themaxbang/MRIYA/pictures/mriya_02.jpeg

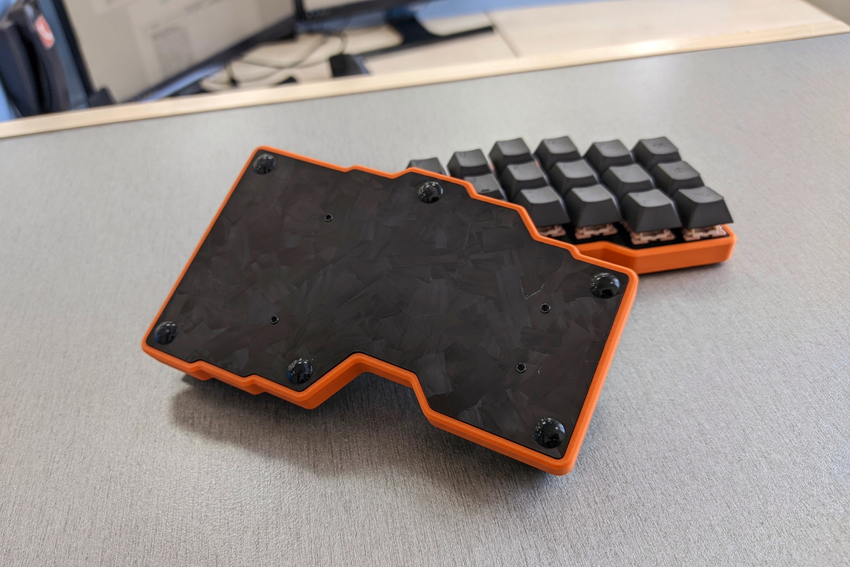
pictures/mriya_02.jpeg
