themaxbang/MRIYA/pictures/mriya_03.jpeg

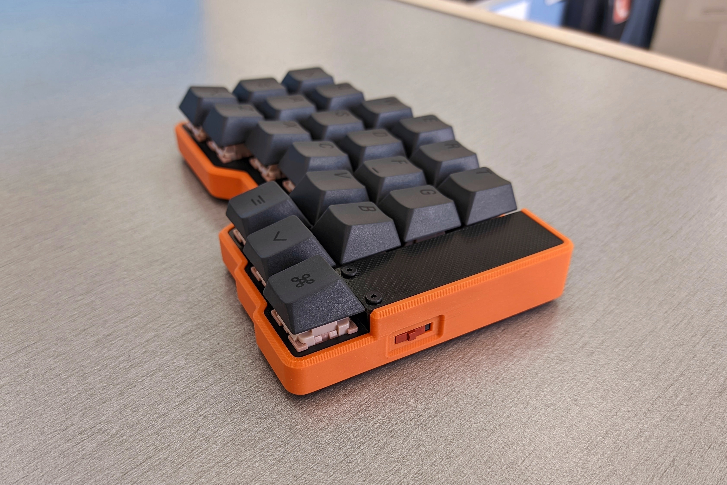
pictures/mriya_03.jpeg
