themaxbang/MRIYA/pictures/mriya_04.jpeg

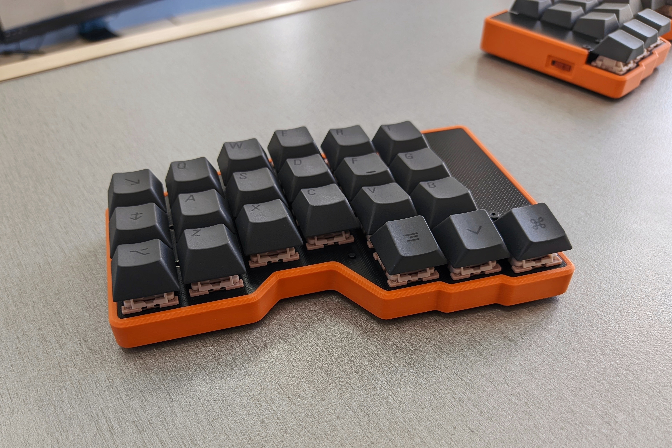
pictures/mriya_04.jpeg
