themaxbang/MRIYA/pictures/mriya_06.jpeg

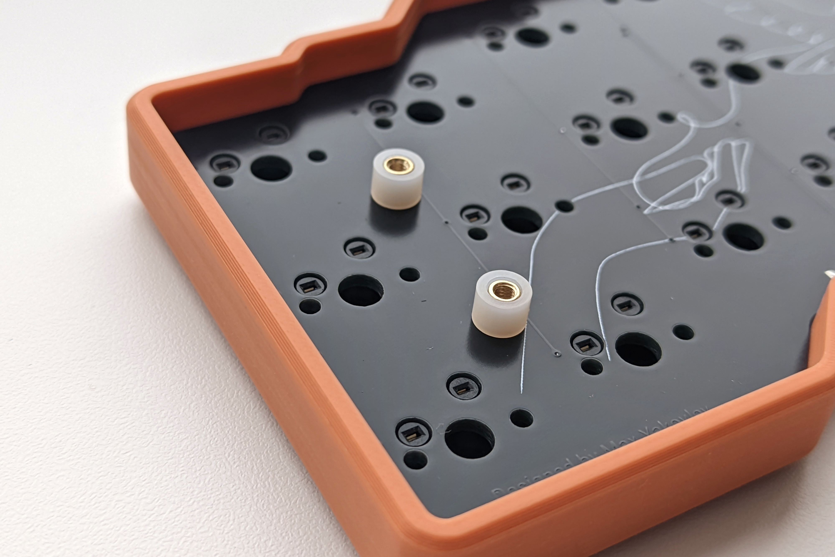
pictures/mriya_06.jpeg
