themaxbang/MRIYA/pictures/mriya_07.jpeg

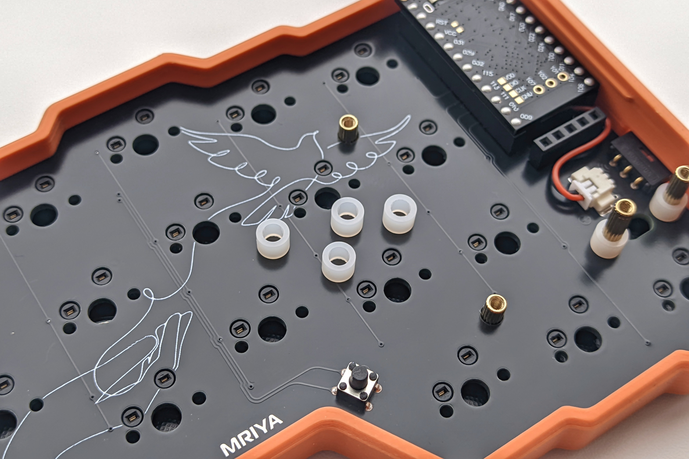
pictures/mriya_07.jpeg
