themaxbang/MRIYA/pictures/mriya_08.jpeg

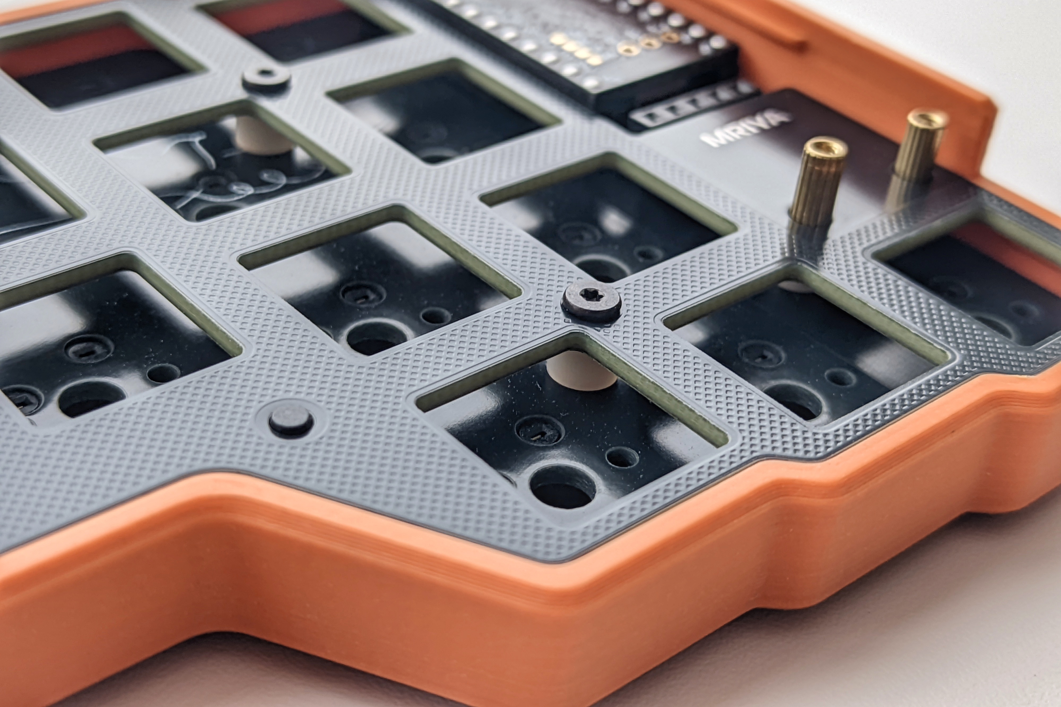
pictures/mriya_08.jpeg
