themaxbang/MRIYA/pictures/mriya_09.jpeg

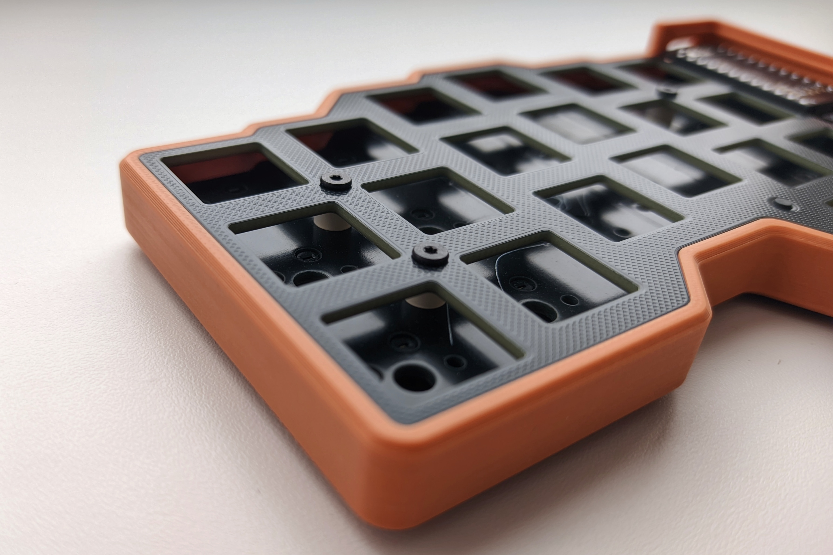
pictures/mriya_09.jpeg
