themaxbang/MRIYA/pictures/mriya_10.jpeg

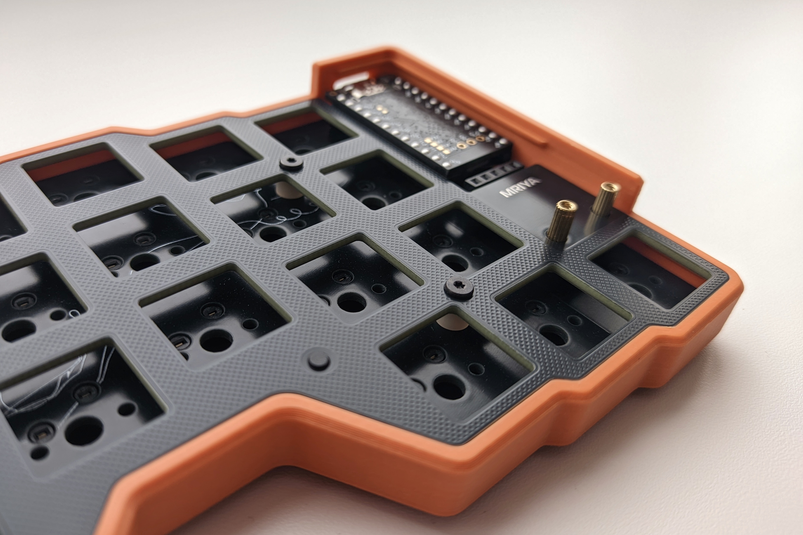
pictures/mriya_10.jpeg
