themaxbang/MRIYA/pictures/mriya_11.jpeg

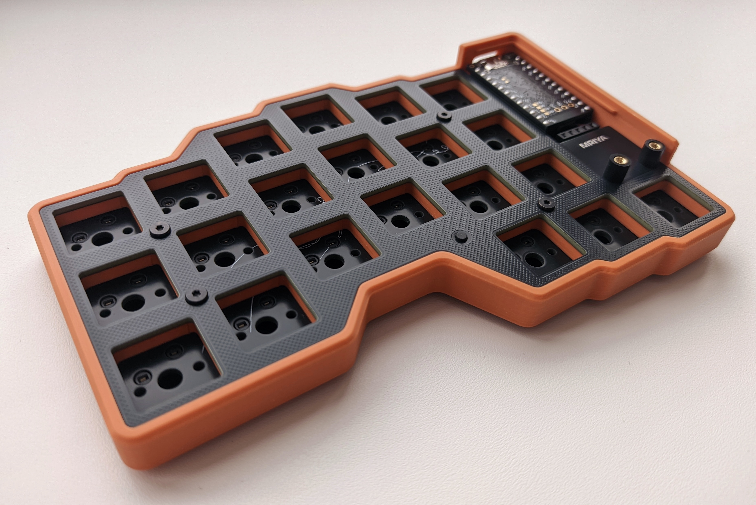
pictures/mriya_11.jpeg
