themaxbang/MRIYA/pictures/mriya_12.jpeg

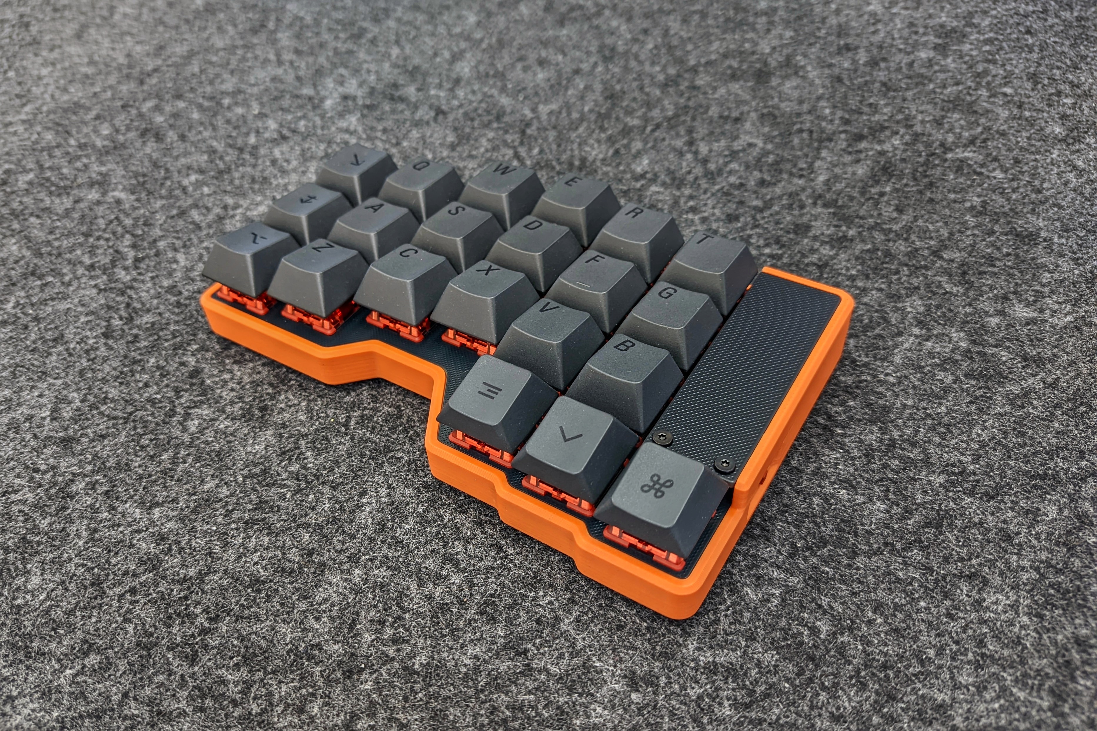
pictures/mriya_12.jpeg
