themaxbang/MRIYA/pictures/mriya_13.jpeg

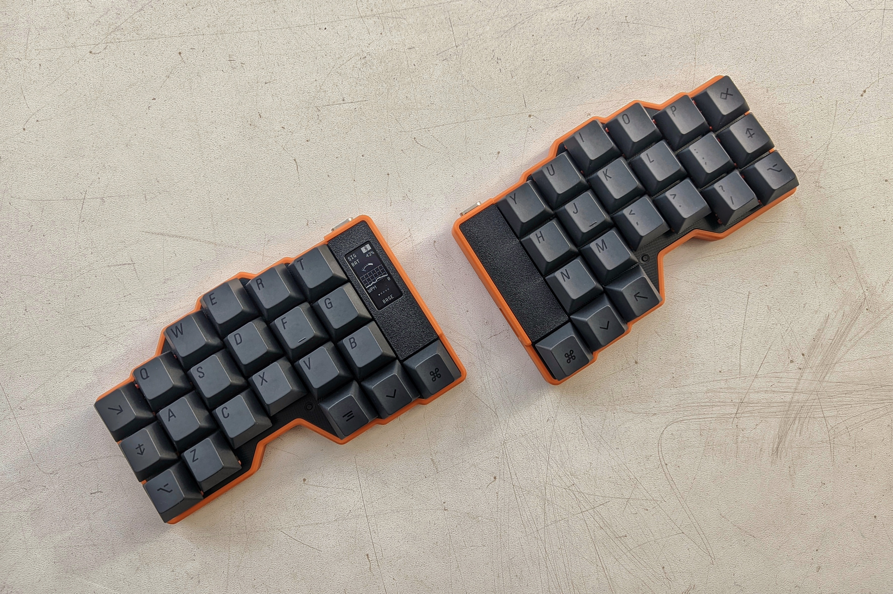
pictures/mriya_13.jpeg
