themaxbang/MRIYA/pictures/mriya_14.jpeg

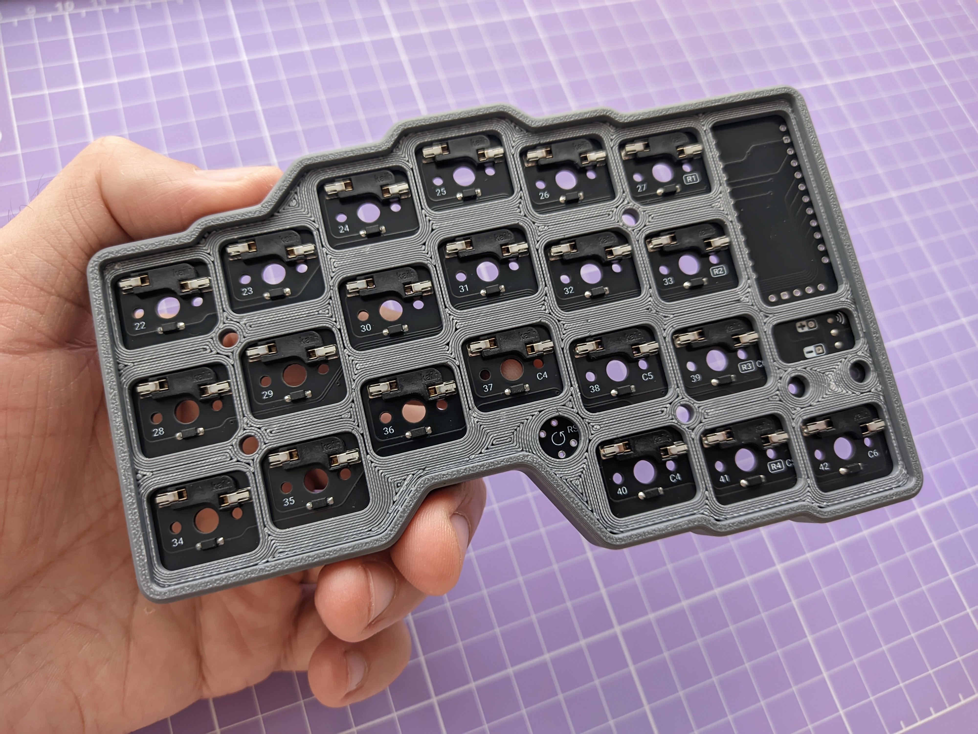
pictures/mriya_14.jpeg
