themaxbang/MRIYA/renders/mriya-bsi-10h-molex.png

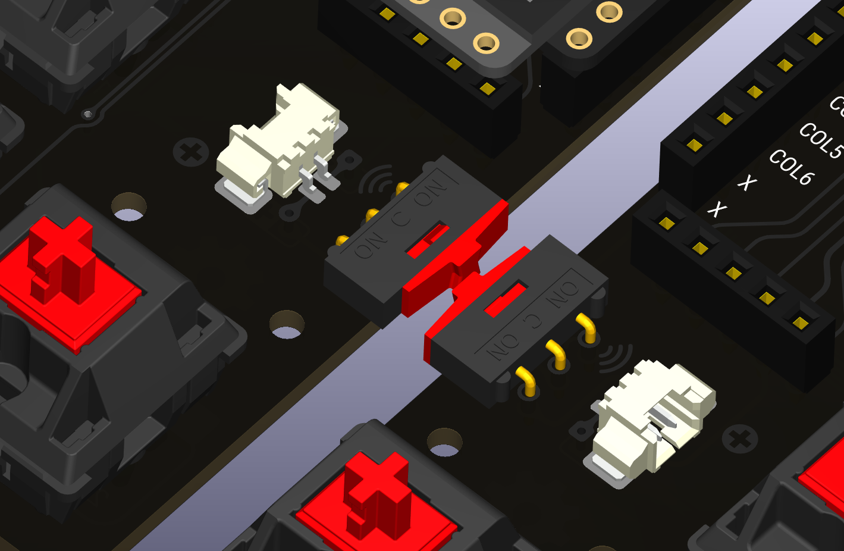
renders/mriya-bsi-10h-molex.png
