themaxbang/MRIYA/renders/mriya-mcu-cover.png

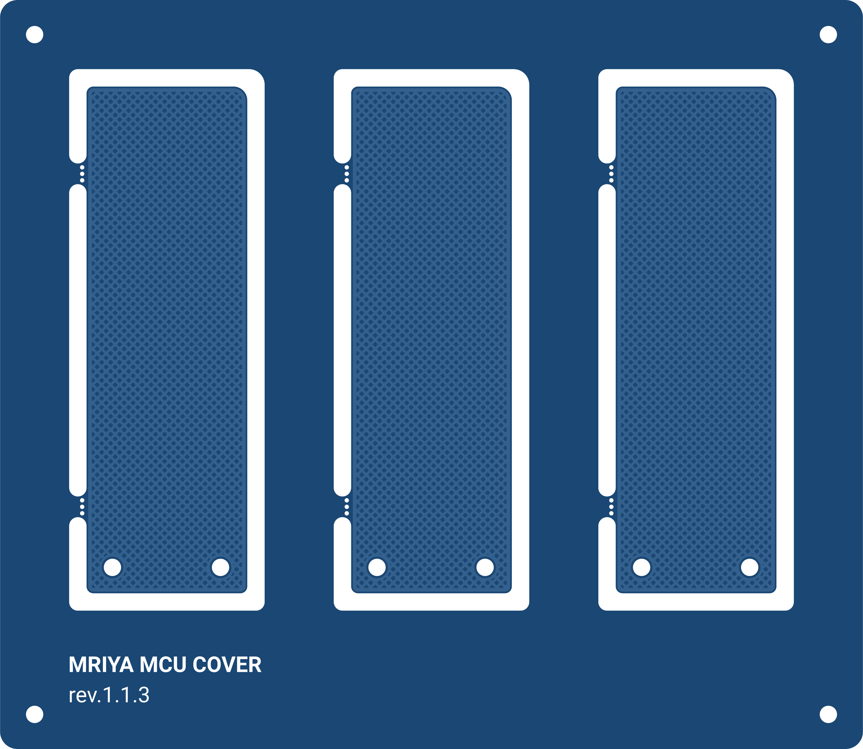
renders/mriya-mcu-cover.png
