themaxbang/MRIYA/case/CNC (not tested)/02 mcu cover/mriya-cnc-display-cover-v1.01.step

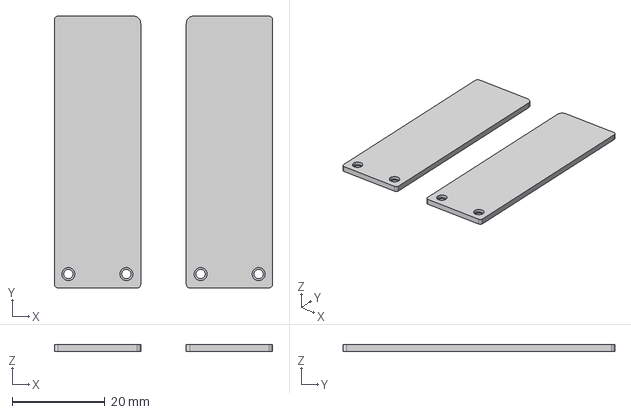
[picture p40: CAD file, 2026-02-08]
case/CNC (not tested)/02 mcu cover/mriya-cnc-display-cover-v1.01.step
47.0 x 58.6 x 1.50 mm
