themaxbang/MRIYA/case/CNC (not tested)/03 top plate/mriya-cnc-top-plate-v.1.01.step

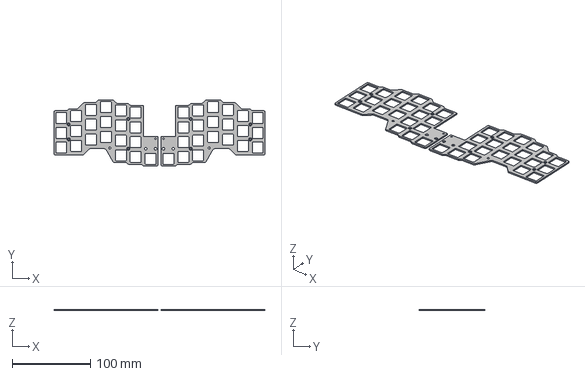
[picture p41: CAD file, 2026-02-08]
case/CNC (not tested)/03 top plate/mriya-cnc-top-plate-v.1.01.step
269.3 x 84.4 x 1.50 mm
