themaxbang/MRIYA/case/CNC (not tested)/04 bottom plate/mriya-cnc-bottom-plate-v.1.01.step

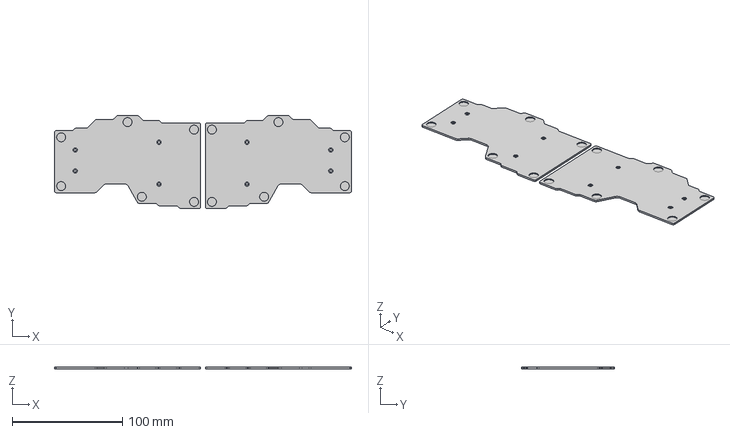
[picture p42: CAD file, 2026-02-08]
case/CNC (not tested)/04 bottom plate/mriya-cnc-bottom-plate-v.1.01.step
269.3 x 84.4 x 1.50 mm
