themaxbang/MRIYA/case/CNC/02 mcu cover/mriya-cnc-mcu-cover.step

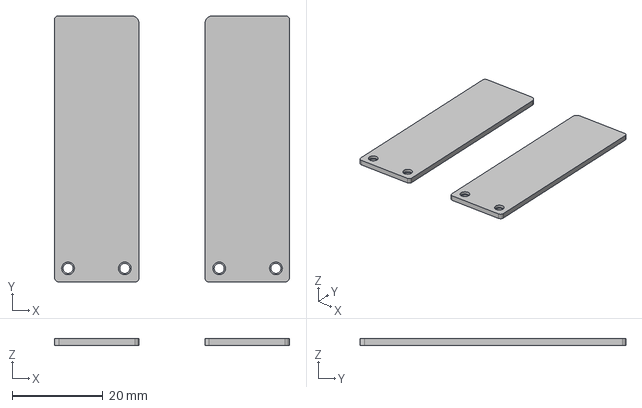
[picture p43: CAD file, 2024-07-14]
case/CNC/02 mcu cover/mriya-cnc-mcu-cover.step
51.8 x 58.6 x 1.50 mm
