themaxbang/MRIYA/pcb/mriya-pcb/mriya3D/niceview v1.step

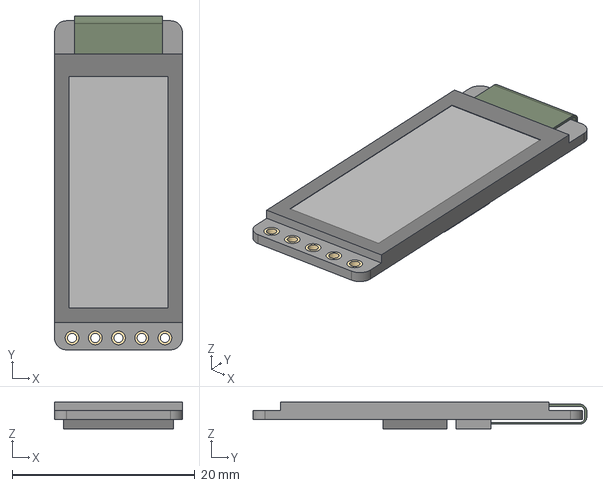
[picture p44: CAD file, 2026-02-08]
pcb/mriya-pcb/mriya3D/niceview v1.step
14.0 x 36.5 x 2.90 mm
