themaxbang/MRIYA/pcb/mriya-pcb/mriya3D/nice!nano v2.step

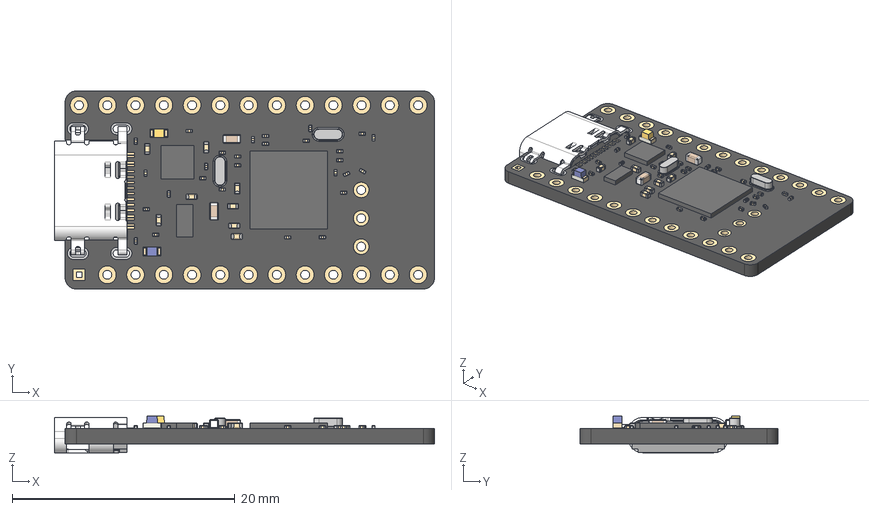
[picture p45: CAD file, 2026-02-08]
pcb/mriya-pcb/mriya3D/nice!nano v2.step
34.2 x 17.8 x 3.28 mm
nice!nano v1.0
SSOP16
LED_0603_1608Metric_ON
LED_0603_1608Metric_ON_1
Crystal Oscillator
Crystal Oscillator_1
usb4520-03-0-a_1
C0201 x 21
C0402 x 8
C0201_1 x 7
