themaxbang/MRIYA/pcb/mriya-pcb/mriya3D/Tact Switch 5.5mm.step

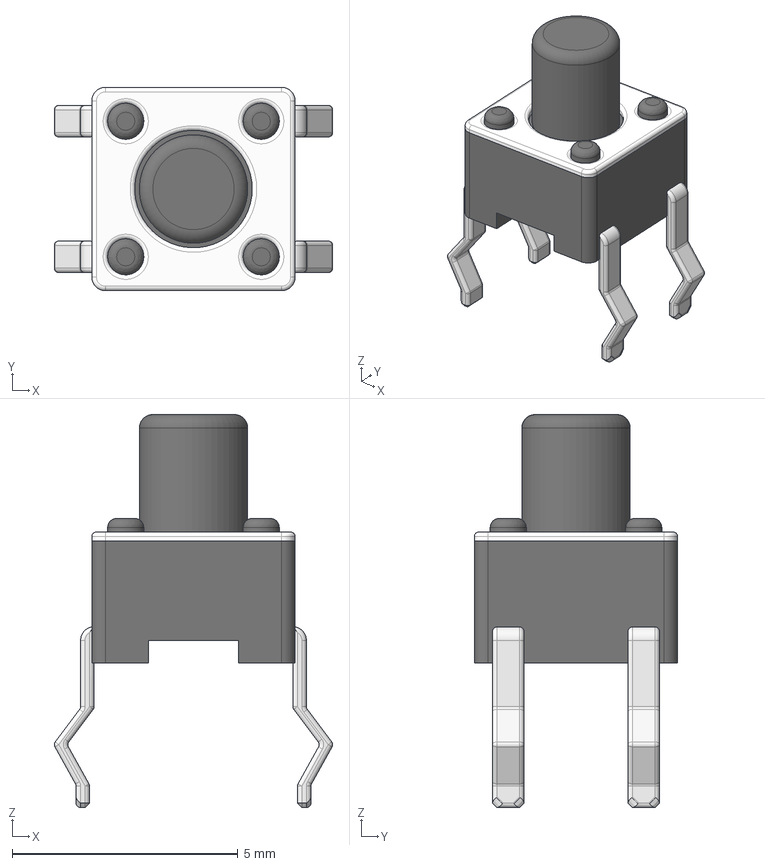
[picture p46: CAD file, 2026-02-08]
pcb/mriya-pcb/mriya3D/Tact Switch 5.5mm.step
6.16 x 4.50 x 8.70 mm
