themaxbang/MRIYA/pcb/mriya-pcb/mriya3D/nice!view.step

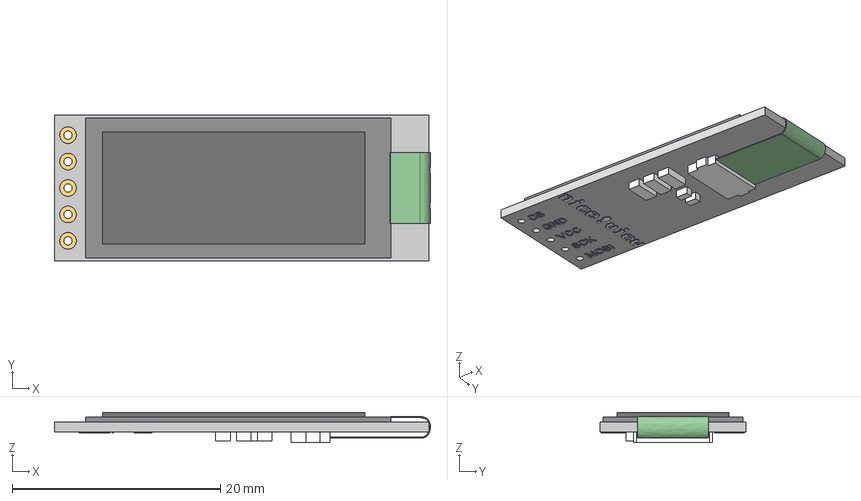
[picture p47: CAD file, 2026-02-08]
pcb/mriya-pcb/mriya3D/nice!view.step
36.1 x 14.0 x 2.90 mm
