themaxbang/MRIYA/pcb/mriya-pcb/mriya3D/12-Pin Header - Female - 2.54mm.step

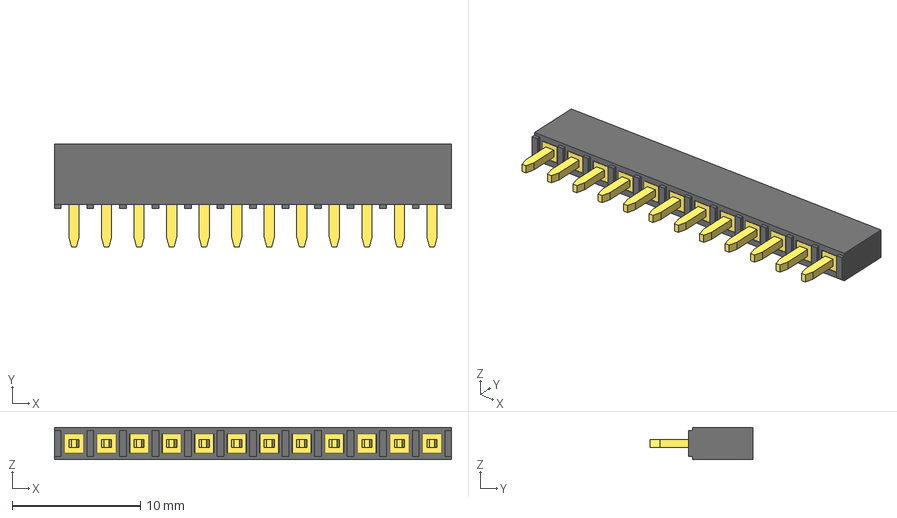
[picture p48: CAD file, 2023-04-26]
pcb/mriya-pcb/mriya3D/12-Pin Header - Female - 2.54mm.step
31.0 x 8.00 x 2.50 mm
