themaxbang/MRIYA/pcb/mriya-pcb/mriya3D/Mini Slide Switch Right Angled 10x2,5mm v1.stp

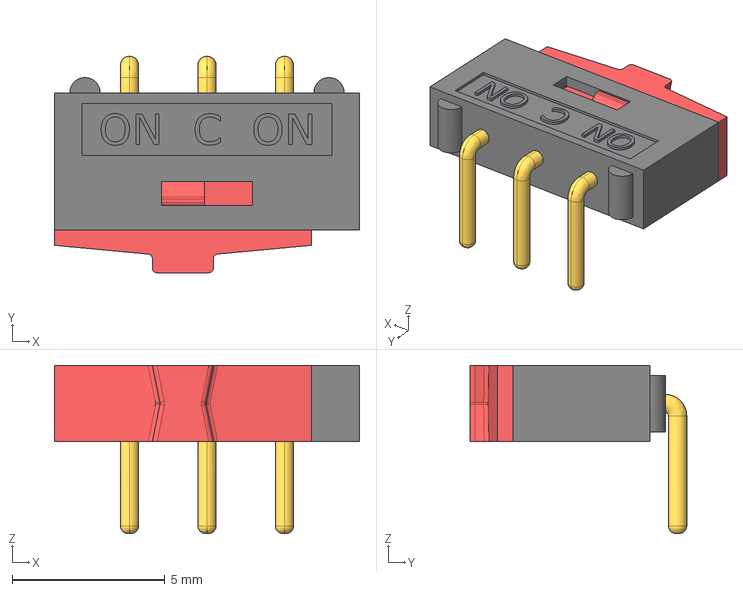
[picture p49: CAD file, 2023-04-26]
pcb/mriya-pcb/mriya3D/Mini Slide Switch Right Angled 10x2,5mm v1.stp
10.0 x 7.10 x 5.51 mm
