themaxbang/MRIYA/pcb/mriya-pcb/mriya3D/MX Series-Cherry Key.step

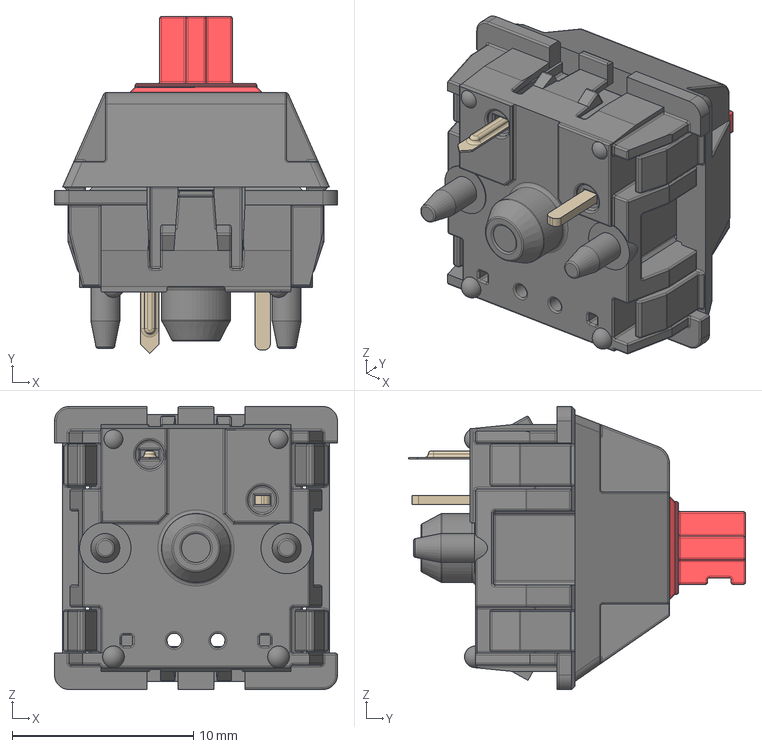
[picture p50: CAD file, 2023-04-26]
pcb/mriya-pcb/mriya3D/MX Series-Cherry Key.step
15.6 x 18.6 x 15.6 mm
