themaxbang/MRIYA/pcb/mriya-pcb/mriya3D/Slide_Red_Switch_crooked.step

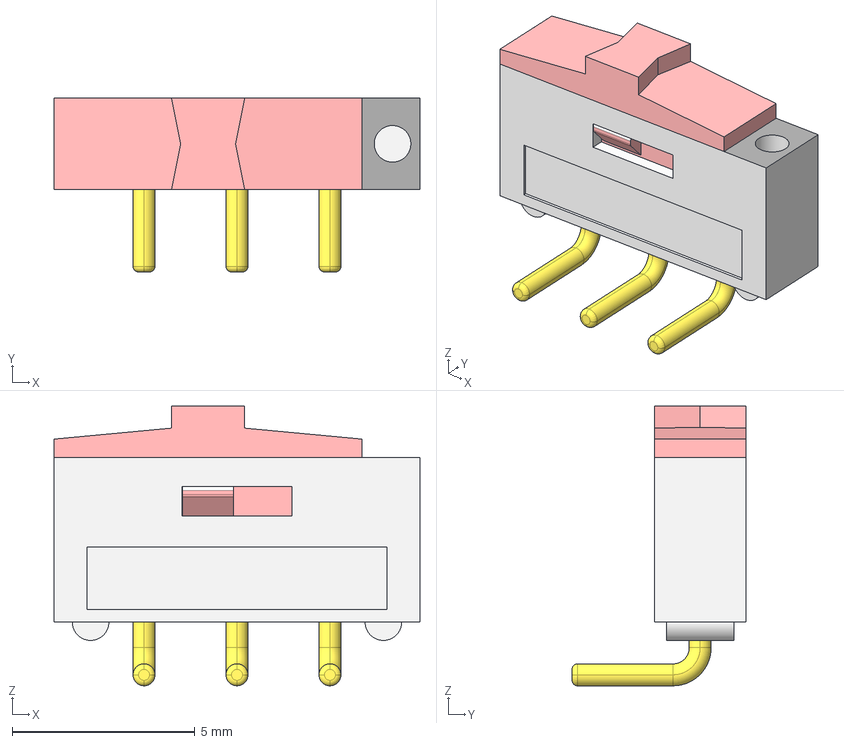
[picture p52: CAD file, 2023-04-26]
pcb/mriya-pcb/mriya3D/Slide_Red_Switch_crooked.step
10.0 x 4.75 x 7.64 mm
Pins
Pins002
Pins001
