themaxbang/MRIYA/pcb/mriya-pcb/mriya3D/D_SOD-123.step

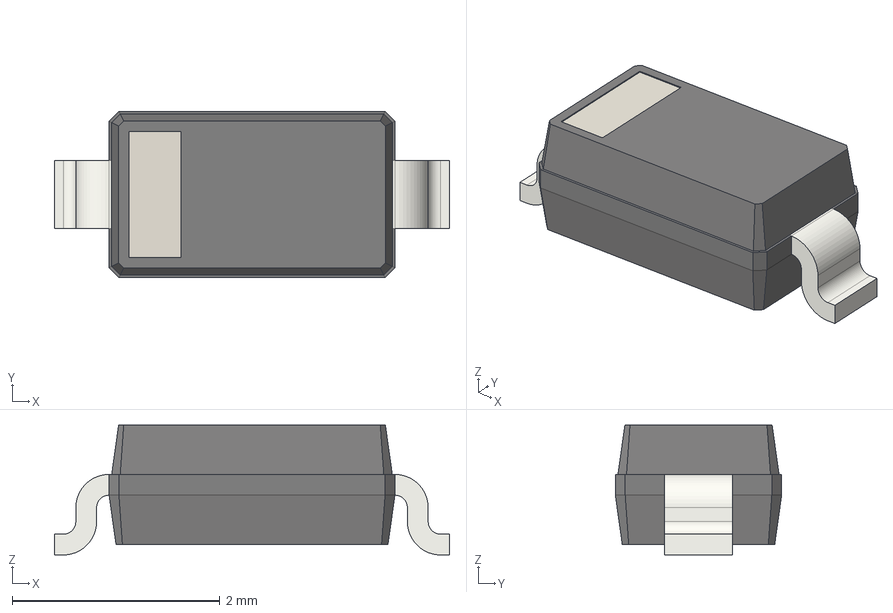
[picture p53: CAD file, 2023-04-26]
pcb/mriya-pcb/mriya3D/D_SOD-123.step
3.80 x 1.60 x 1.25 mm
