themaxbang/MRIYA/pcb/mriya-pcb/mriya3D/Kailh-CherryMX-Socket.step

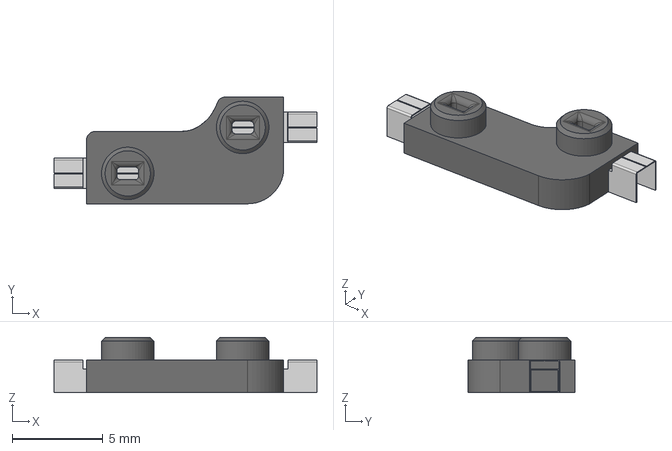
[picture p54: CAD file, 2023-04-26]
pcb/mriya-pcb/mriya3D/Kailh-CherryMX-Socket.step
14.5 x 5.89 x 3.05 mm
