themaxbang/MRIYA/pcb/mriya-pcb/mriya3D/5-Pin Header - Female - 2.54mm.step

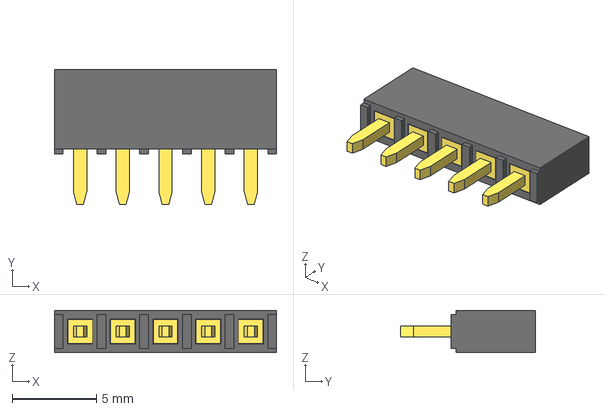
[picture p55: CAD file, 2023-04-26]
pcb/mriya-pcb/mriya3D/5-Pin Header - Female - 2.54mm.step
13.2 x 8.00 x 2.50 mm
