themaxbang/MRIYA/pcb/mriya-pcb/mriya3D/female rounded header.stp

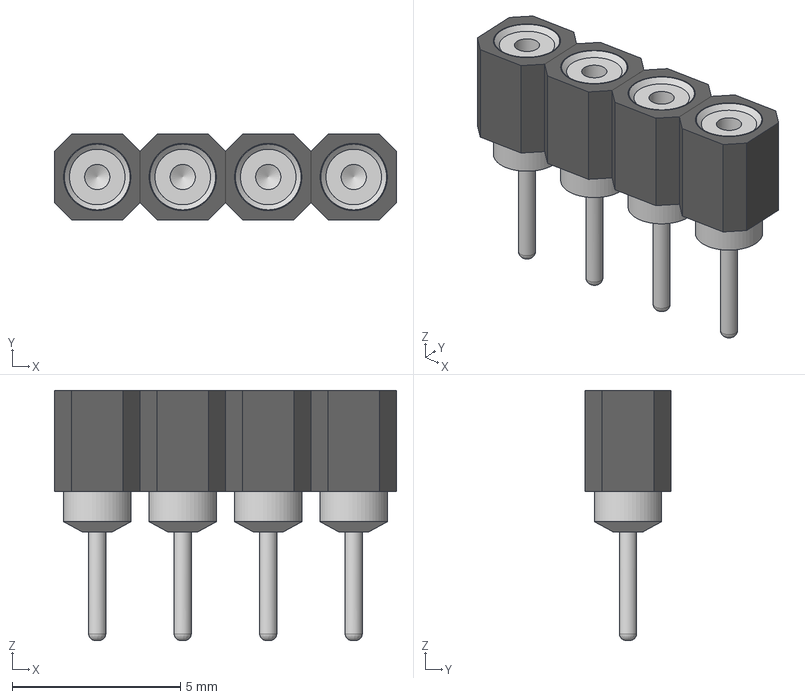
[picture p56: CAD file, 2023-04-26]
pcb/mriya-pcb/mriya3D/female rounded header.stp
10.2 x 2.54 x 7.43 mm
