themaxbang/MRIYA/pcb/mriya-pcb/mriya3D/PG1350-socket.STEP

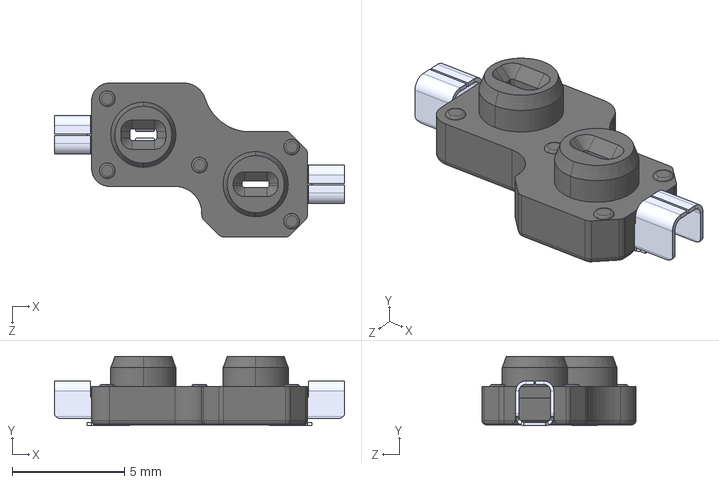
[picture p57: CAD file, 2023-04-26]
pcb/mriya-pcb/mriya3D/PG1350-socket.STEP
12.9 x 3.09 x 6.85 mm
pin x 2
socket
