themaxbang/MRIYA/pcb/mriya-pcb/mriya3D/Kailh Polia.step

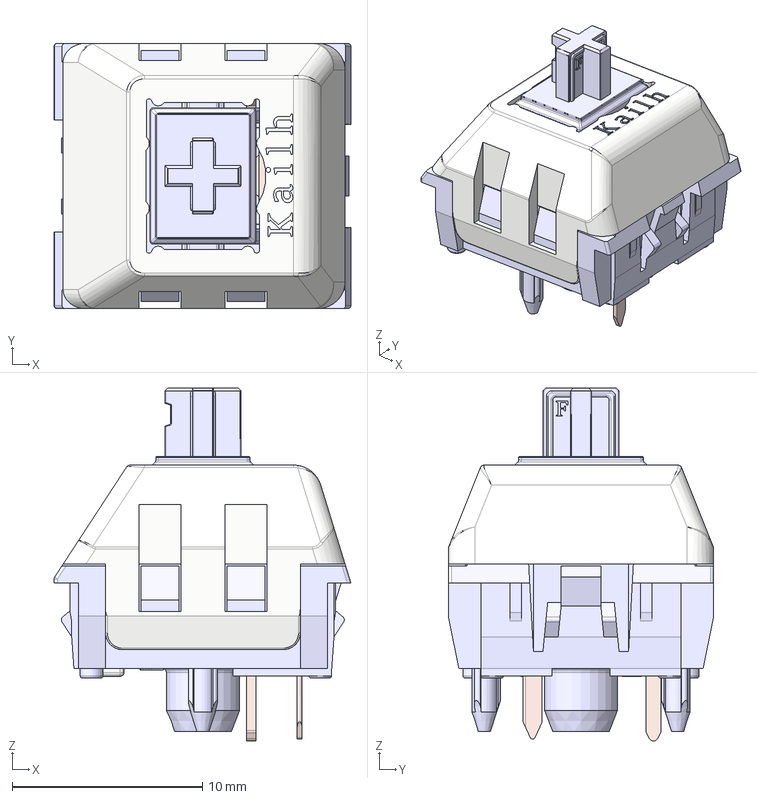
[picture p58: CAD file, 2023-04-26]
pcb/mriya-pcb/mriya3D/Kailh Polia.step
15.6 x 14.0 x 18.5 mm
Housing
ThickContact
SpringContact
Stem
Lid
