themaxbang/MRIYA/pcb/mriya-pcb/mriya3D/D_SOD-123 Soldered.step

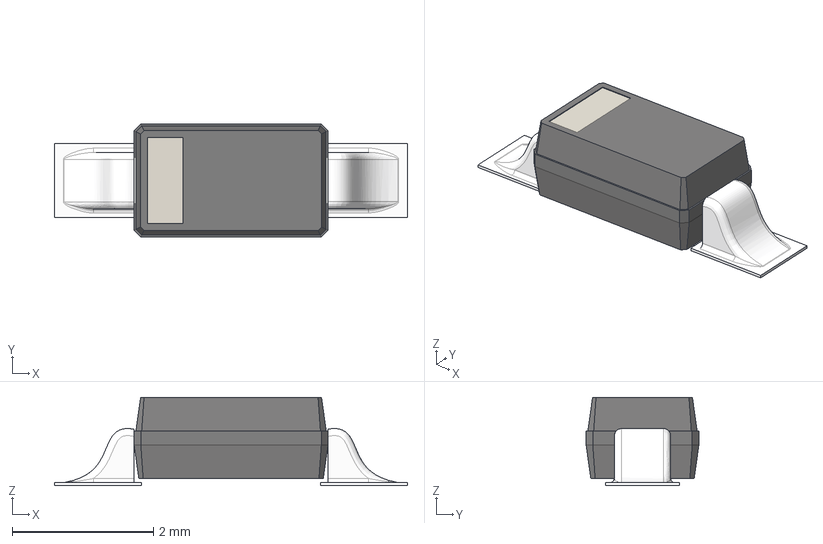
[picture p59: CAD file, 2023-04-26]
pcb/mriya-pcb/mriya3D/D_SOD-123 Soldered.step
5.01 x 1.60 x 1.25 mm
