themaxbang/MRIYA/pcb/mriya-pcb/mriya3D/Kailh Hotswap.step

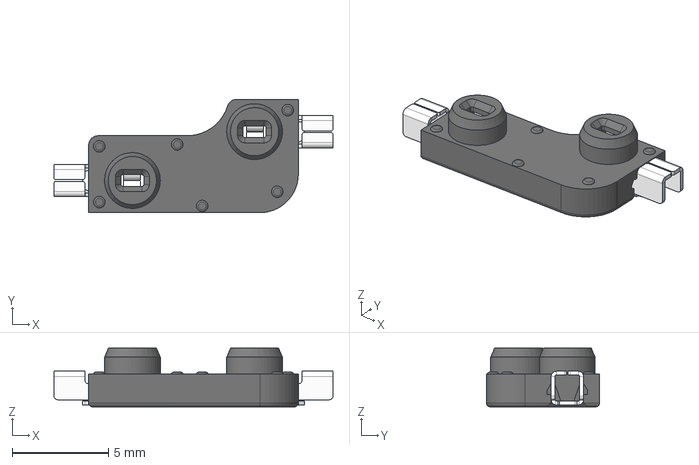
[picture p60: CAD file, 2023-04-26]
pcb/mriya-pcb/mriya3D/Kailh Hotswap.step
14.5 x 5.89 x 3.05 mm
Contact x 2
